zzattack/munia/enclosure/n64-connector.png

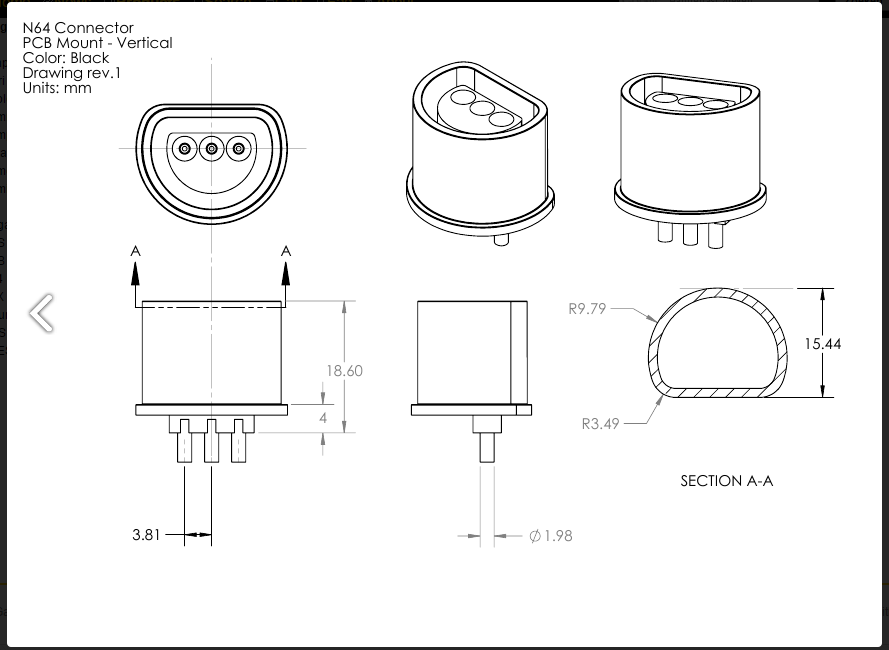
enclosure/n64-connector.png
