zzattack/munia/enclosure/ngc-connector.png

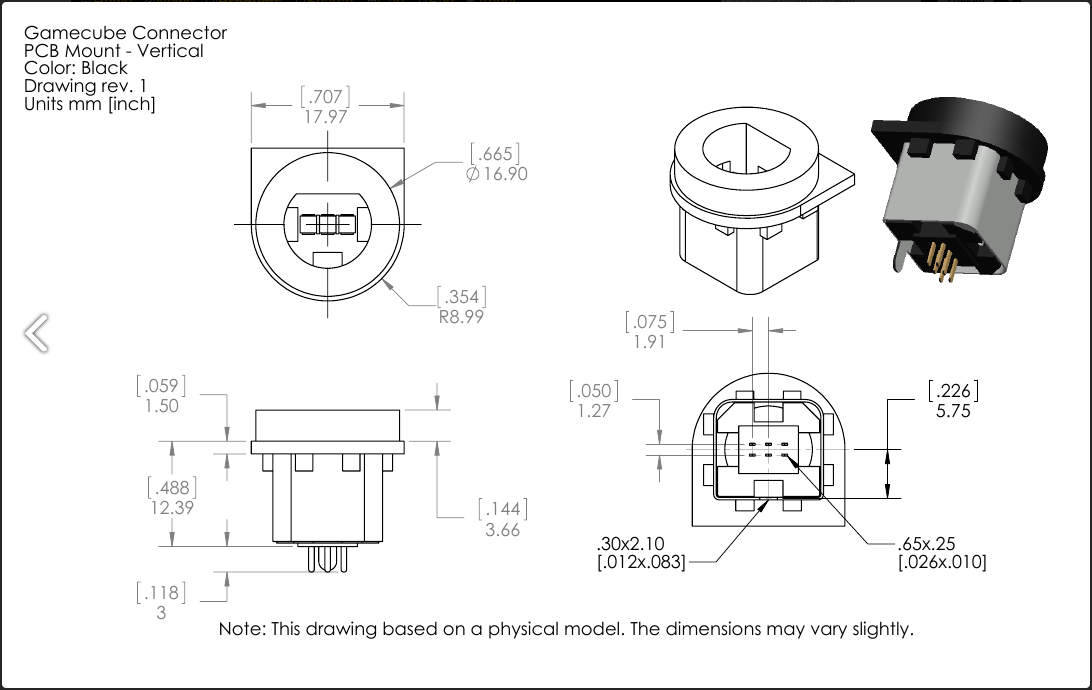
enclosure/ngc-connector.png
