zzattack/munia/MUNIA-win/MUNIA/Resources/munia256.png

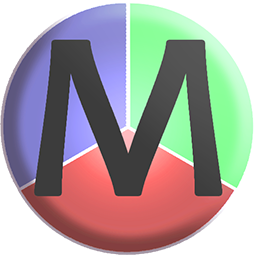
MUNIA-win/MUNIA/Resources/munia256.png
