zzattack/munia/MUNIA-win/MUNIA/Resources/reassign.png

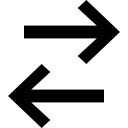
MUNIA-win/MUNIA/Resources/reassign.png
