zzattack/munia/munia_io/static_global/img/content/arduino_mapper.png

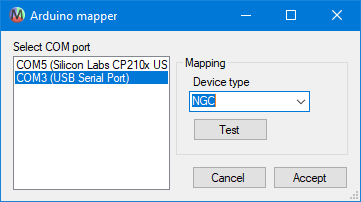
munia_io/static_global/img/content/arduino_mapper.png
