zzattack/munia/munia_io/static_global/img/content/code-illustration.png

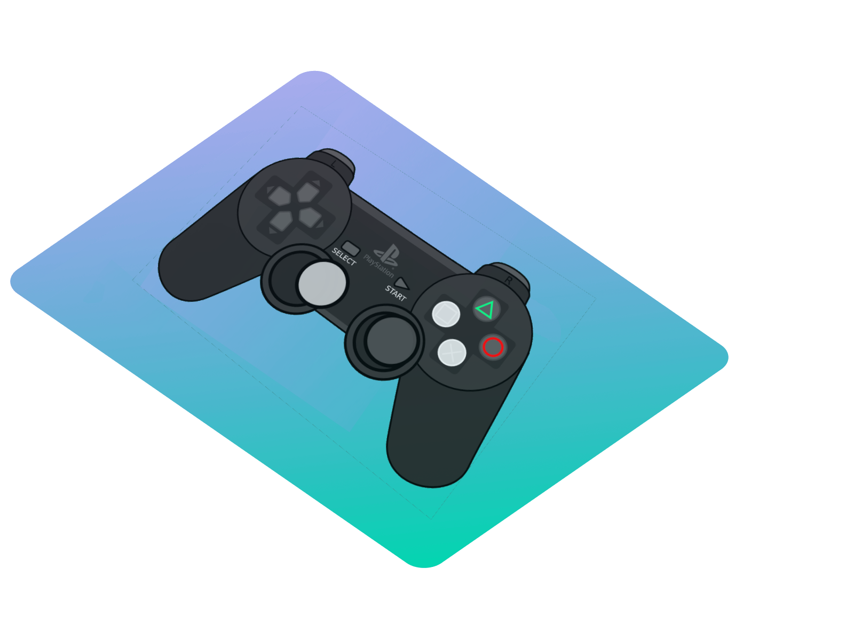
munia_io/static_global/img/content/code-illustration.png
