zzattack/munia/munia_io/static_global/img/content/consoles.png

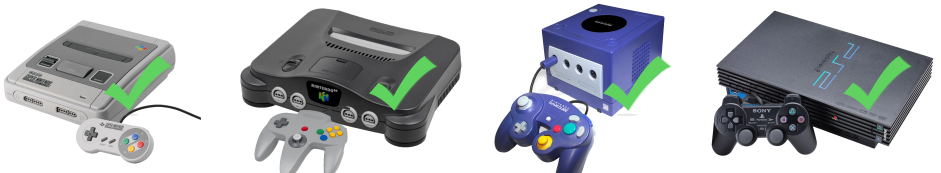
munia_io/static_global/img/content/consoles.png
