zzattack/munia/munia_io/static_global/img/content/device.png

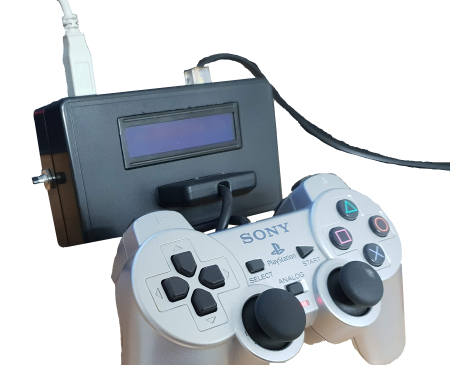
munia_io/static_global/img/content/device.png
