zzattack/munia/munia_io/static_global/img/content/lag_compensation.png

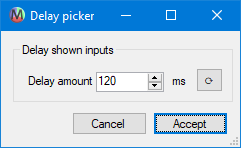
munia_io/static_global/img/content/lag_compensation.png
