zzattack/munia/munia_io/static_global/img/content/munia-n64_device.png

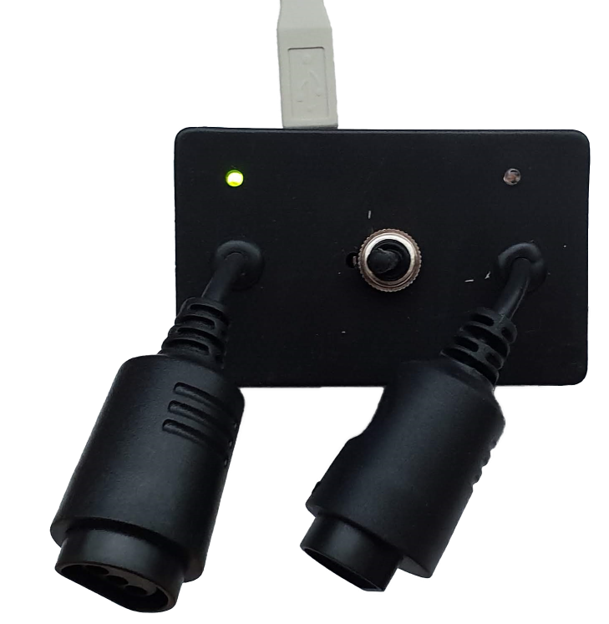
munia_io/static_global/img/content/munia-n64_device.png
