zzattack/munia/munia_io/static_global/img/content/munia.png

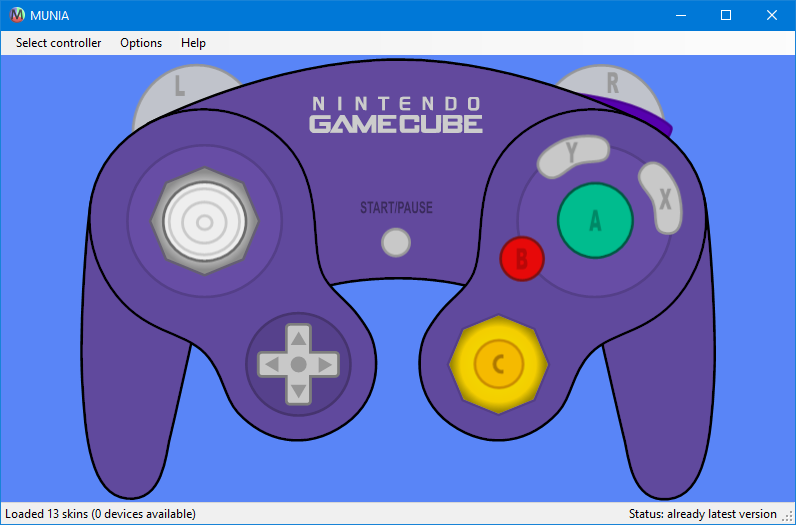
munia_io/static_global/img/content/munia.png
