zzattack/munia/munia_io/static_global/img/content/munia_device.png

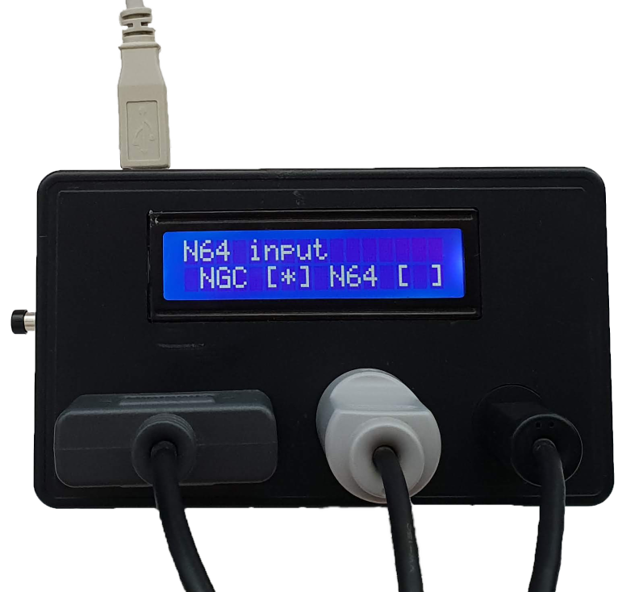
munia_io/static_global/img/content/munia_device.png
