zzattack/munia/munia_io/static_global/img/content/musia_device.png

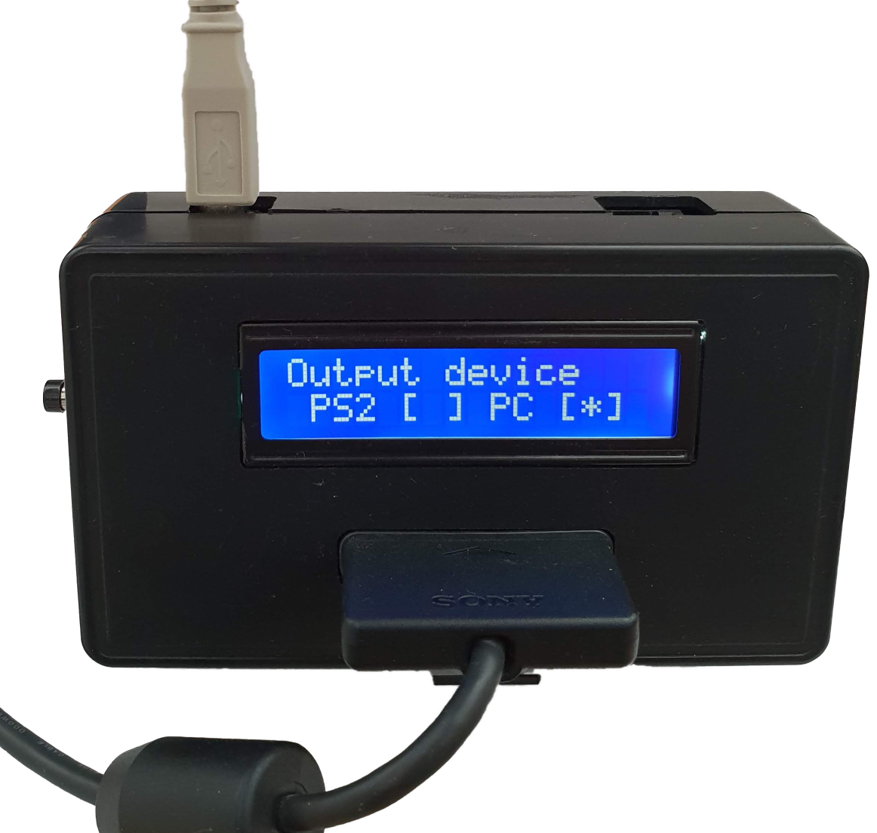
munia_io/static_global/img/content/musia_device.png
