zzattack/munia/munia_io/static_global/img/content/skin_gamecube.png

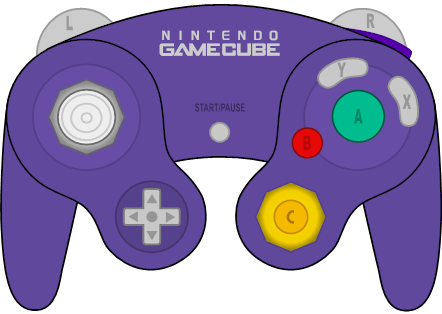
munia_io/static_global/img/content/skin_gamecube.png
