zzattack/munia/munia_io/static_global/img/content/skin_n64.png

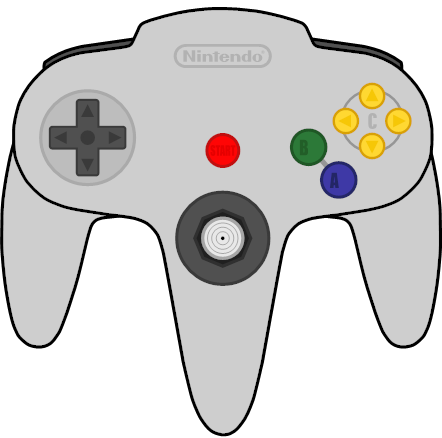
munia_io/static_global/img/content/skin_n64.png
