zzattack/munia/munia_io/static_global/img/content/skin_n64_compact.png

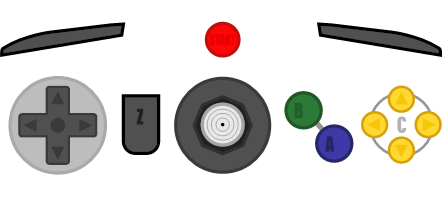
munia_io/static_global/img/content/skin_n64_compact.png
