zzattack/munia/munia_io/static_global/img/content/skin_ps2_compact.png

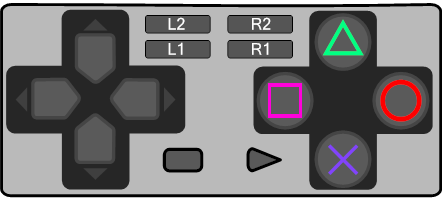
munia_io/static_global/img/content/skin_ps2_compact.png
