zzattack/munia/munia_io/static_global/img/content/skin_snes.png

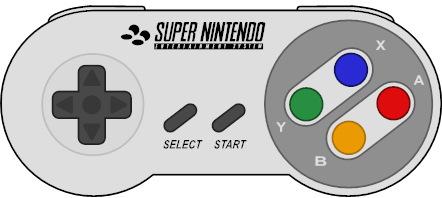
munia_io/static_global/img/content/skin_snes.png
