zzattack/munia/munia_io/static_global/img/content/skin_snes_compact.png

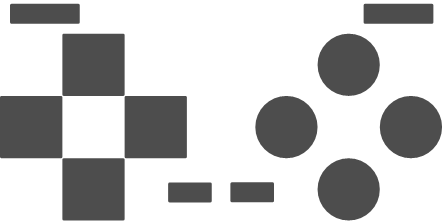
munia_io/static_global/img/content/skin_snes_compact.png
