zzattack/munia/firmware/munia.X/gamecube.c

#include "gamecube.h"
#include "hardware.h"
#include "globals.h"
#include <usb/usb_device_hid.h>
#include "gamepad.h"
#include "asm_decl.h"
#include "fakeout.h"
#include "menu.h"
#include "uarts.h"

ngc_packet_t joydata_ngc_last_raw;

void ngc_tasks() {
    if (pollNeeded && (in_menu || (config.input_ngc && config.output_mode != output_ngc))) {
        USBDeviceTasks();
        di();
        ngc_poll();
        // waste some more instructions before sampling
        _delay(40);
        asm("lfsr 0, _sample_buff+25"); // setup FSR0
        ngc_sample();
        asm("movff FSR0L, _sample_w+0"); // update sample_w
    }
    
    if (packets.ngc_test) {
        if (!in_menu && config.output_mode == output_ngc && !config.input_ngc) {
            ngc_fakeout_test();
            WRITETIMER3(65000); // schedule next fake poll soon
        }
        else ngc_handle_packet();
        packets.ngc_test = false;
    }
    
    INTCONbits.IOCIF = 0; // don't bother with stuff that happened in the meantime
    ei();

    if (packets.ngc_avail) {
        // see if this packet is equal to the last transmitted one, and if so, discard it
        // also when in menu, menu_tasks will clear bit
        if (in_menu) return;
        else if (memcmp(&joydata_ngc_raw, &joydata_ngc_last_raw, sizeof(ngc_packet_t))) {
            // dbgs("new packets.ngc_avail\n");
            // new, changed packet available; unpack if faking and send over usb
            
            if (config.input_sources & input_ngc && config.output_mode == output_n64) {
                // dbgs("ngc_create_n64_fake()\n");
                ngc_to_n64();
                fake_unpack((uint8_t*)&joydata_n64_raw, sizeof(n64_packet_t));
            }
        
            else if (config.input_sources & input_ngc && config.output_mode == output_snes) {
                // dbgs("ngc_create_snes_fake()\n");
                ngc_to_snes();
                fake_unpack((uint8_t*)&joydata_snes_raw, sizeof(snes_packet_t));
            }
            
            if (USB_READY && !HIDTxHandleBusy(USBInHandleNGC)) {
                // dbgs("ngc_joydata_createhid()\n");
                ngc_joydata_createhid();
                USBInHandleNGC = HIDTxPacket(HID_EP_NGC, (uint8_t*)&joydata_ngc_usb, sizeof(ngc_packet_t));
            }
            
            // save last packet
            memcpy(&joydata_ngc_last_raw, &joydata_ngc_raw, sizeof(ngc_packet_t));
        }
        packets.ngc_avail = false; // now consumed
    }    
}

void ngc_poll() {
    portc_mask = 0b00000001;
    LATC &= ~portc_mask; // pull down - always call this before CLR() calls
    CLR(); // set data pin to output, making the pin low
    // send 01000000
    //      00000011    
    //      00000010
    LOW(); HIGH(); LOW(); LOW(); LOW(); LOW(); LOW(); LOW(); 
    LOW(); LOW(); LOW(); LOW(); LOW(); LOW(); HIGH(); HIGH(); 
    LOW(); LOW(); LOW(); LOW(); LOW(); LOW(); LOW(); LOW(); 
    
    // stop bit, 2 us
    CLR(); 
    _delay(22);
    SET();// back set to open collector input with pull up
    LATC |= portc_mask; // reset pull up
}

void ngc_handle_packet() {
    // translate samples in sample_buff to joydata_ngc
	uint8_t idx = sample_w - sample_buff;
    // dbgs("ngc packet len: "); dbgsval(idx); dbgs("\n");
    
    // 89 = 24 bits request, 1 stopbit, + 64 bits of data
	if (idx == 89) {        
		uint8_t* w = (uint8_t*)&joydata_ngc_raw;
        
		// bit 0 is not sampled, then 0-23 are request, 24 is stop bit, 25-88 is data
		int8_t* r = (int8_t*)(sample_buff + 25);
		for (uint8_t i = 0; i < sizeof(ngc_packet_t); i++) {
            *w++ = pack_byte(r);
            r += 8;
		}

        packets.ngc_avail = true;
	}
    else if (idx != 8 && idx != 24) { // 8,24 for poll, with no controller attached/fake mode
        // dbgs("ngc unexpected packet len: "); dbgsval(idx); dbgs("\n");
    }
}

void ngc_joydata_createhid() {
    // these are inverted in HID reports
    joydata_ngc_usb = joydata_ngc_raw;
    joydata_ngc_usb.joy_y = -joydata_ngc_usb.joy_y;
    joydata_ngc_usb.c_y = -joydata_ngc_usb.c_y;
    joydata_ngc_usb.hat = hat_lookup_ngc[joydata_ngc_usb.hat];    
}
