zzattack/munia/firmware/MUSIA/lcd.h

#ifndef LCD_H
#define	LCD_H

#include <stdint.h>
#include "circular_buffer.h"

#define LCD_LINES 2
#define LCD_INIT 0b00101000 // for 2 lines
#define LCD_DISPLAY_OFF 0x08
#define LCD_DISPLAY_ON_CURSOR_OFF 0x0C
#define LCD_DISPLAY LCD_DISPLAY_OFF // display off initially

#define SPECIAL_TOCMD 251
#define SPECIAL_TOCHR 250

EXTERNC void lcd_setup();
EXTERNC void lcd_process();
EXTERNC void lcd_command(uint8_t cmd);
EXTERNC void lcd_goto(uint8_t line, uint8_t pos);
#define lcd_clear() lcd_command(0x01)
#define lcd_home() lcd_command(0x80)

EXTERNC void lcd_char(uint8_t chr);
EXTERNC void lcd_string(const char *q);

EXTERNC void lcd_backlight(uint8_t pwm);

#endif	/* LCD_H */
